pu2clr/VFO_SI5351_ARDUINO_SMARTPHONE/source/vfoMobileApplication/www/css/theme/darkBigBackground.png

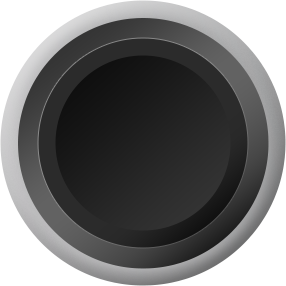
source/vfoMobileApplication/www/css/theme/darkBigBackground.png
