pu2clr/VFO_SI5351_ARDUINO_SMARTPHONE/source/vfoMobileApplication/www/css/theme/lightBigBackground.png

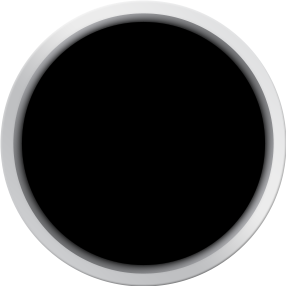
source/vfoMobileApplication/www/css/theme/lightBigBackground.png
