pu2clr/VFO_SI5351_ARDUINO_SMARTPHONE/source/vfoMobileApplication/www/css/theme/lightBigFront.png

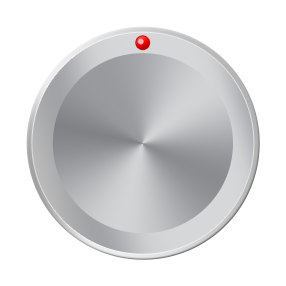
source/vfoMobileApplication/www/css/theme/lightBigFront.png
